DenDen047/WildPose_v1.1/wildpose/hardware/WLDPOSE011 Yaw shaft.SLDPRT

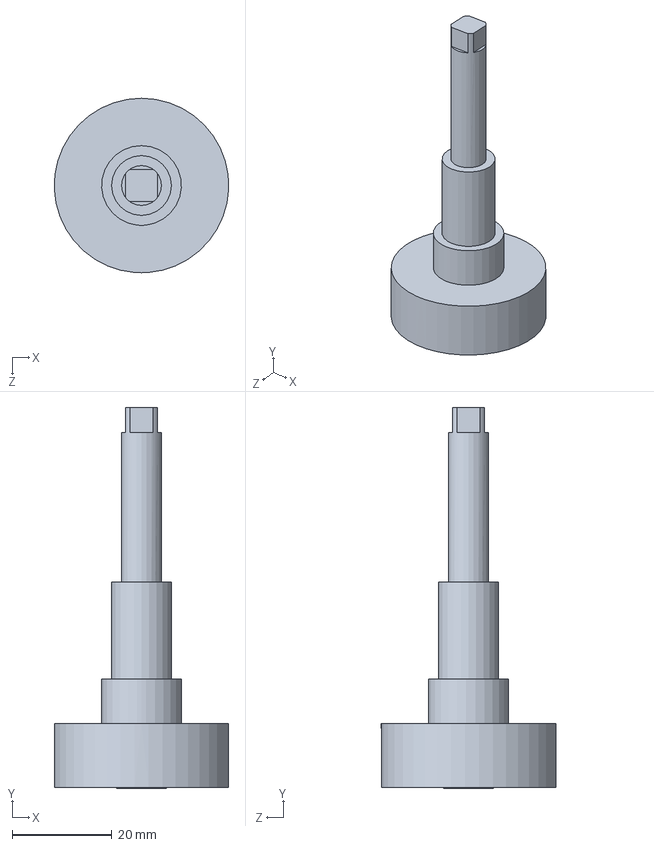
[picture p13: CAD file, 2025-09-01]
wildpose/hardware/WLDPOSE011 Yaw shaft.SLDPRT
35.0 x 76.4 x 35.0 mm
