DenDen047/WildPose_v1.1/wildpose/hardware/WLDPOSE006 Shaft Holder.SLDPRT

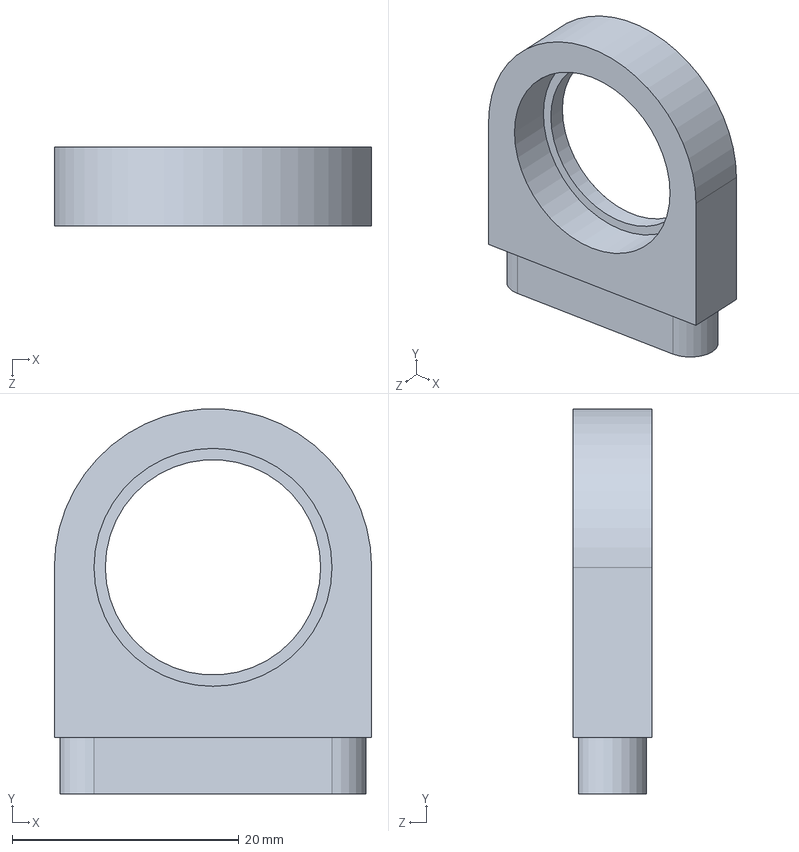
[picture p14: CAD file, 2025-09-01]
wildpose/hardware/WLDPOSE006 Shaft Holder.SLDPRT
28.0 x 34.0 x 7.00 mm
