DenDen047/WildPose_v1.1/wildpose/hardware/Timing Belt 80 T 162.56mm x 6mm.SLDPRT

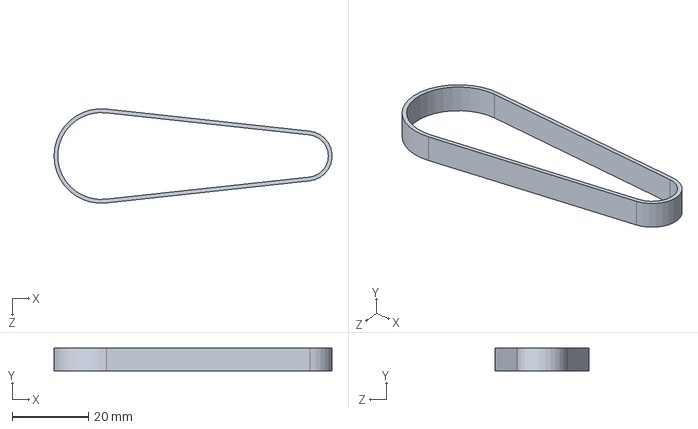
[picture p15: CAD file, 2025-09-01]
wildpose/hardware/Timing Belt 80 T 162.56mm x 6mm.SLDPRT
72.9 x 6.00 x 24.7 mm
