DenDen047/WildPose_v1.1/wildpose/hardware/HandleRod.SLDPRT

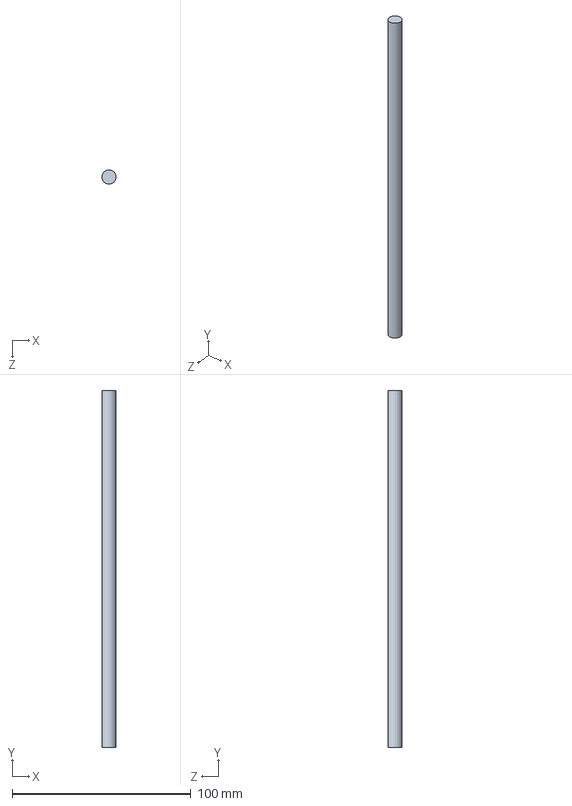
[picture p16: CAD file, 2025-09-01]
wildpose/hardware/HandleRod.SLDPRT
8.00 x 200.0 x 8.00 mm
