DenDen047/WildPose_v1.1/wildpose/hardware/Motor Mount.SLDPRT

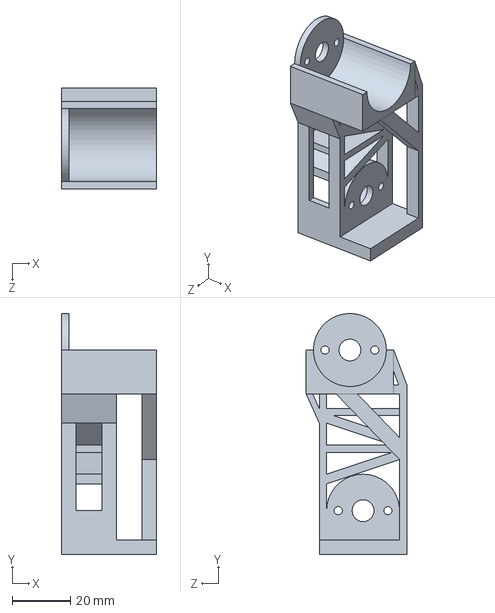
[picture p17: CAD file, 2025-09-01]
wildpose/hardware/Motor Mount.SLDPRT
32.5 x 82.5 x 34.5 mm
