DenDen047/WildPose_v1.1/wildpose/hardware/Pitch Encoder Holder (Printed).SLDPRT

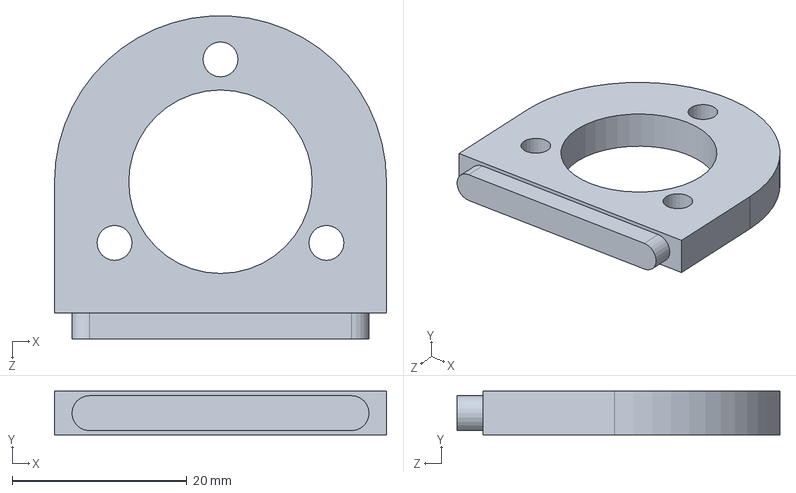
[picture p18: CAD file, 2025-09-01]
wildpose/hardware/Pitch Encoder Holder (Printed).SLDPRT
38.0 x 5.00 x 37.0 mm
