DenDen047/WildPose_v1.1/wildpose/hardware/Motor Belt.SLDPRT

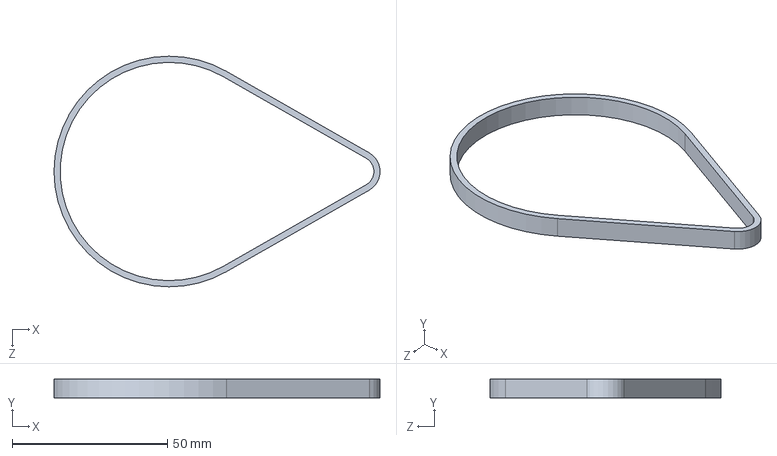
[picture p19: CAD file, 2025-09-01]
wildpose/hardware/Motor Belt.SLDPRT
105.0 x 6.00 x 74.3 mm
