DenDen047/WildPose_v1.1/wildpose/hardware/Xavier Holder.SLDPRT

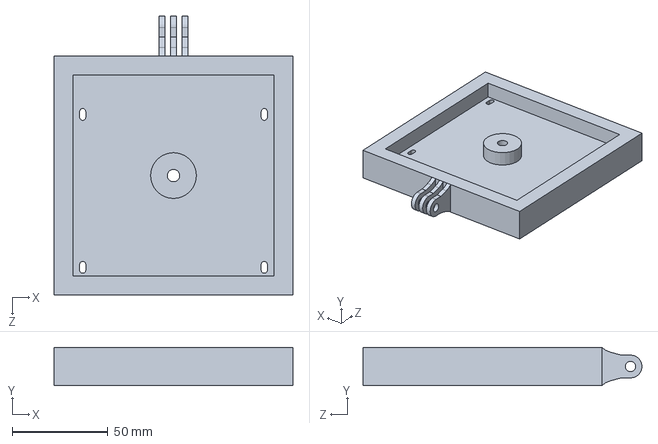
[picture p20: CAD file, 2025-09-01]
wildpose/hardware/Xavier Holder.SLDPRT
125.0 x 20.0 x 146.0 mm
