DenDen047/WildPose_v1.1/wildpose/hardware/WLDPOSE008 Pitch Shaft Connector v2.SLDPRT

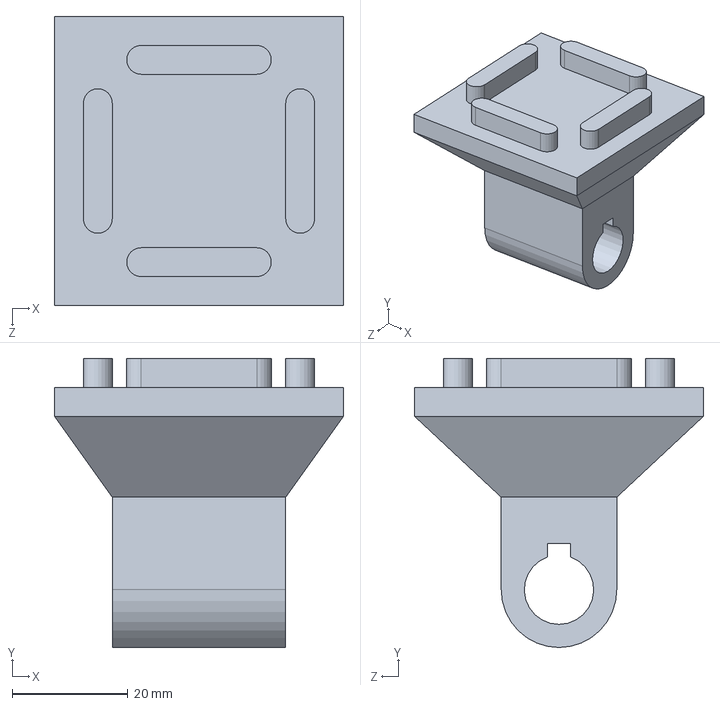
[picture p21: CAD file, 2025-09-01]
wildpose/hardware/WLDPOSE008 Pitch Shaft Connector v2.SLDPRT
50.0 x 50.0 x 50.0 mm
