DenDen047/WildPose_v1.1/wildpose/hardware/WLDPOSE003 Base Shaft Support Slot.SLDPRT

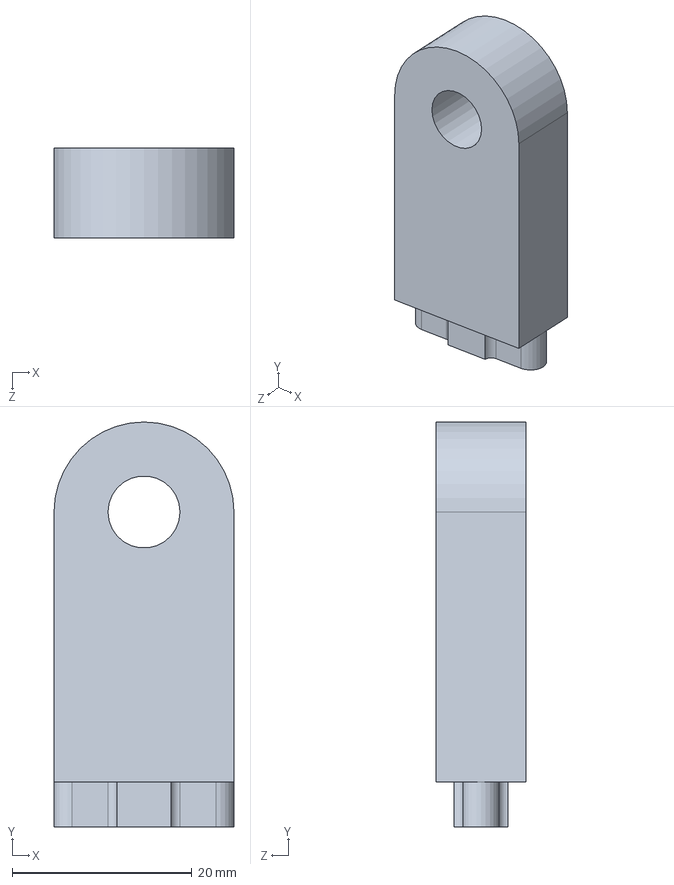
[picture p22: CAD file, 2025-09-01]
wildpose/hardware/WLDPOSE003 Base Shaft Support Slot.SLDPRT
20.0 x 45.0 x 10.0 mm
