DenDen047/WildPose_v1.1/wildpose/hardware/Ximea Holder.SLDPRT

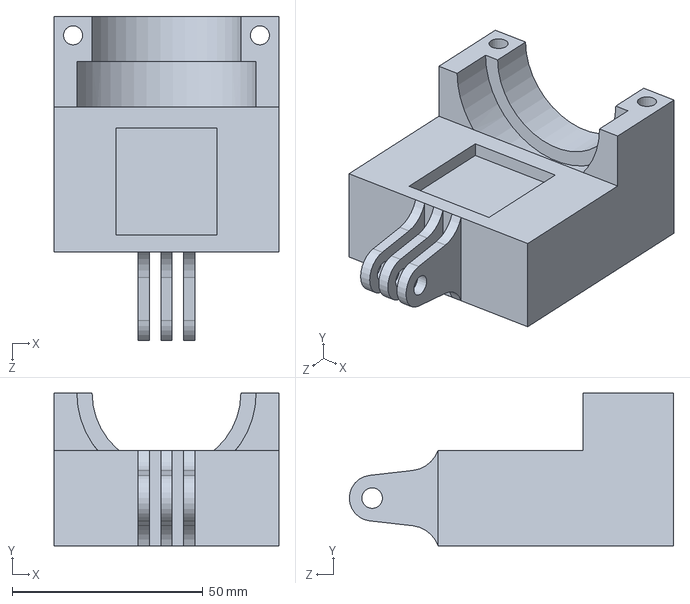
[picture p23: CAD file, 2025-09-01]
wildpose/hardware/Ximea Holder.SLDPRT
59.0 x 40.0 x 85.1 mm
