DenDen047/WildPose_v1.1/wildpose/hardware/Lens Support.SLDPRT

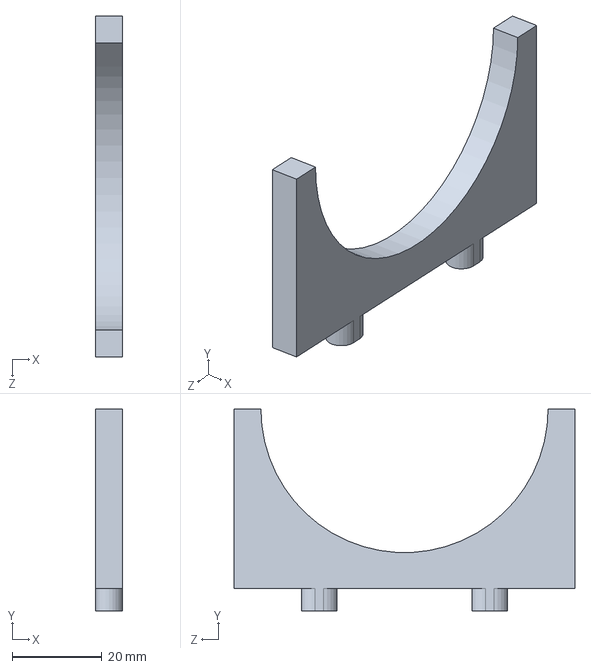
[picture p24: CAD file, 2025-09-01]
wildpose/hardware/Lens Support.SLDPRT
6.00 x 45.0 x 76.0 mm
