DenDen047/WildPose_v1.1/wildpose/hardware/Lens.SLDPRT

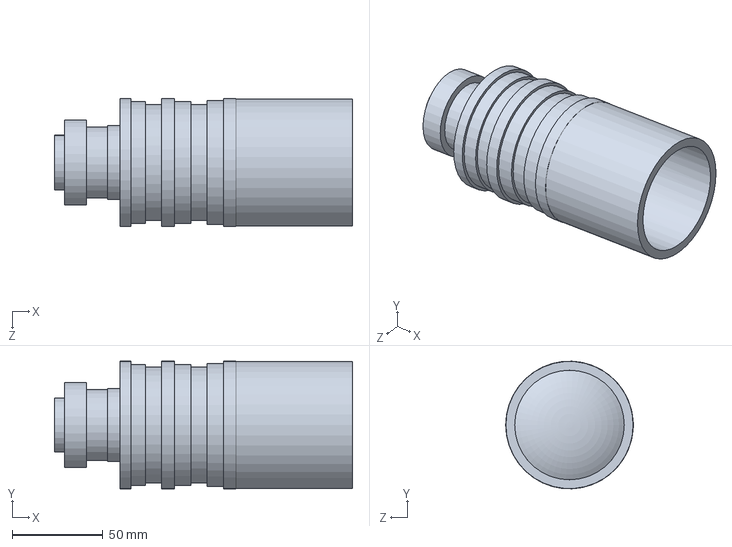
[picture p25: CAD file, 2025-09-01]
wildpose/hardware/Lens.SLDPRT
164.0 x 70.2 x 70.3 mm
