DenDen047/WildPose_v1.1/wildpose/hardware/WLDPOSE002 Base Bilot.SLDPRT

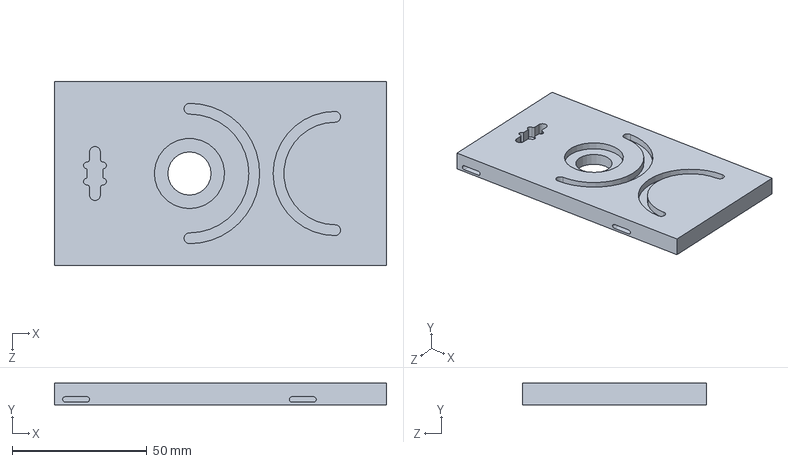
[picture p26: CAD file, 2025-09-01]
wildpose/hardware/WLDPOSE002 Base Bilot.SLDPRT
123.0 x 8.00 x 68.0 mm
