DenDen047/WildPose_v1.1/wildpose/hardware/WLDPOSE004 Bearing Holder.SLDPRT

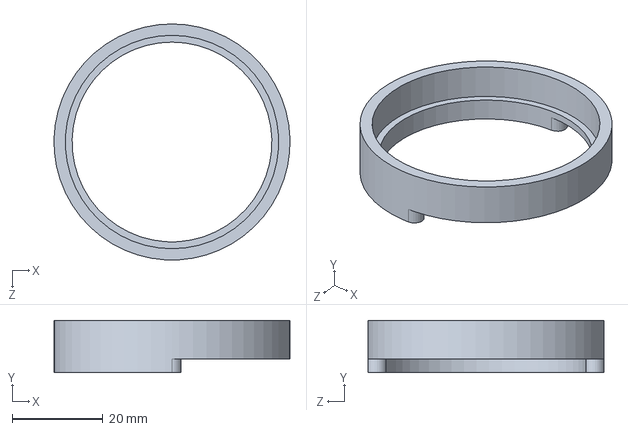
[picture p27: CAD file, 2025-09-01]
wildpose/hardware/WLDPOSE004 Bearing Holder.SLDPRT
52.0 x 11.5 x 52.0 mm
