DenDen047/WildPose_v1.1/wildpose/hardware/Zimea Camera MQ022CG-CM.SLDPRT

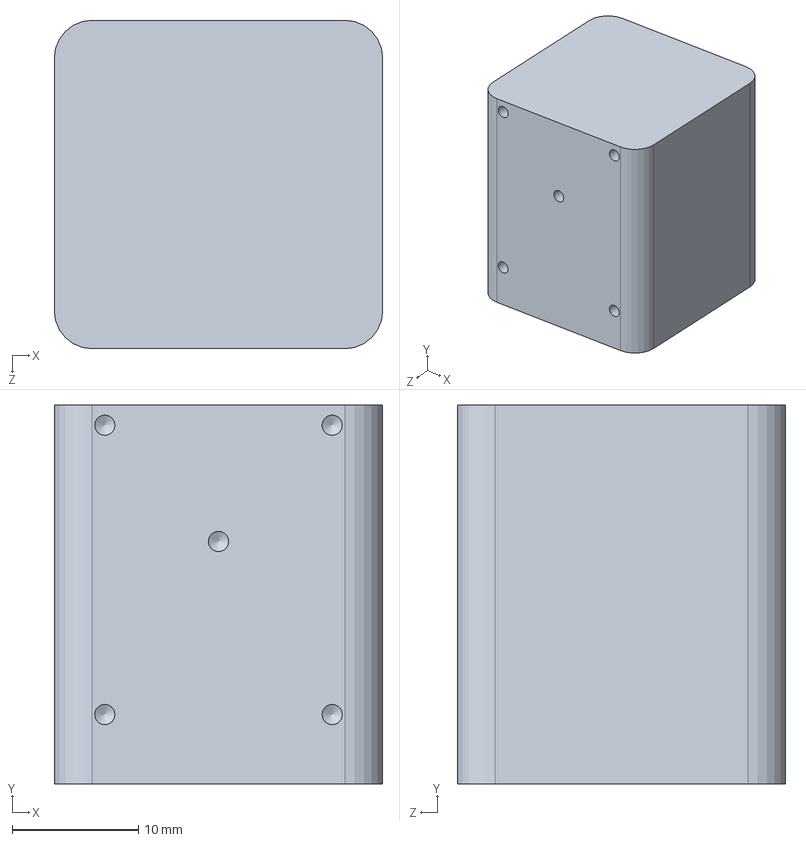
[picture p28: CAD file, 2025-09-01]
wildpose/hardware/Zimea Camera MQ022CG-CM.SLDPRT
26.0 x 30.0 x 26.0 mm
