DenDen047/WildPose_v1.1/wildpose/hardware/Screen Mount.SLDPRT

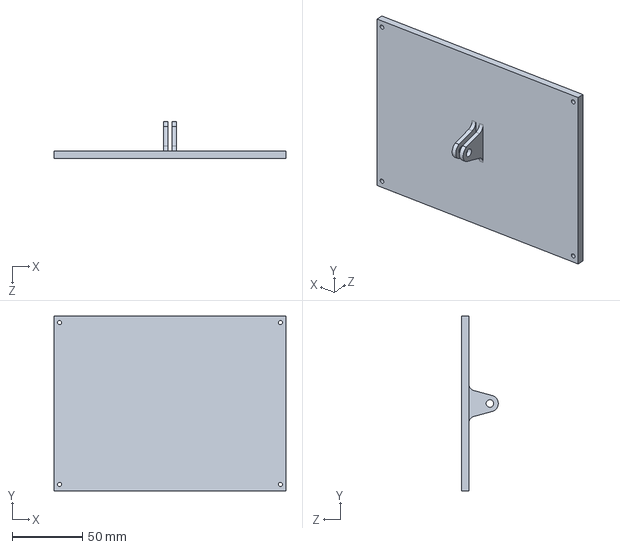
[picture p29: CAD file, 2025-09-01]
wildpose/hardware/Screen Mount.SLDPRT
164.9 x 124.2 x 26.0 mm
