DenDen047/WildPose_v1.1/wildpose/hardware/Camera Mount.SLDPRT

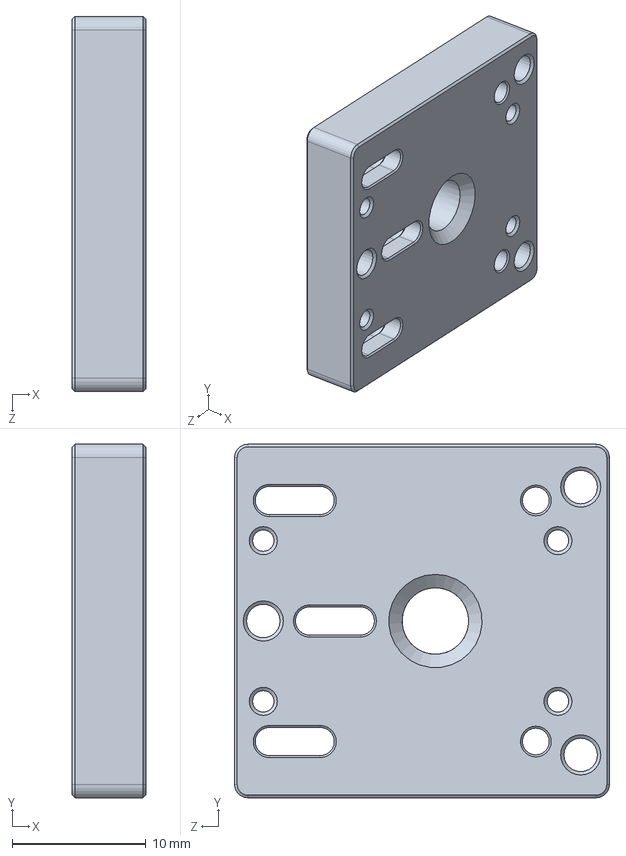
[picture p30: CAD file, 2025-09-01]
wildpose/hardware/Camera Mount.SLDPRT
5.50 x 26.4 x 28.0 mm
