DenDen047/WildPose_v1.1/wildpose/hardware/18 T 2.032mm P , 6mm W Pulley.SLDPRT

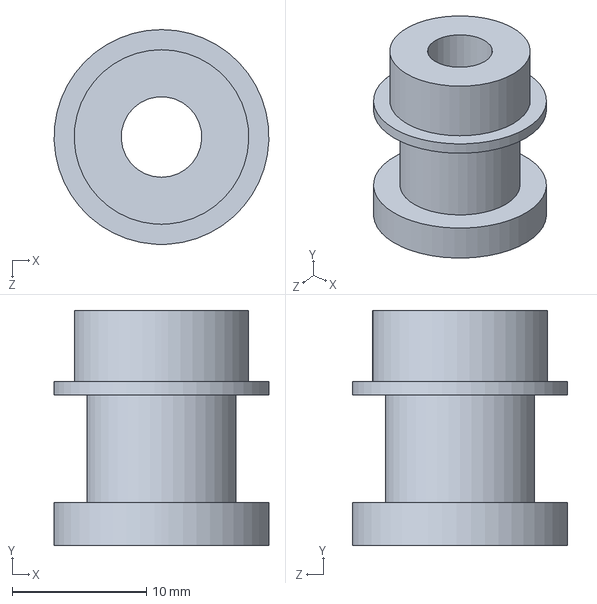
[picture p31: CAD file, 2025-09-01]
wildpose/hardware/18 T 2.032mm P , 6mm W Pulley.SLDPRT
16.0 x 17.5 x 16.0 mm
