DenDen047/WildPose_v1.1/wildpose/hardware/25d-metal-gearmotor-75-99-encoder.step.SLDPRT

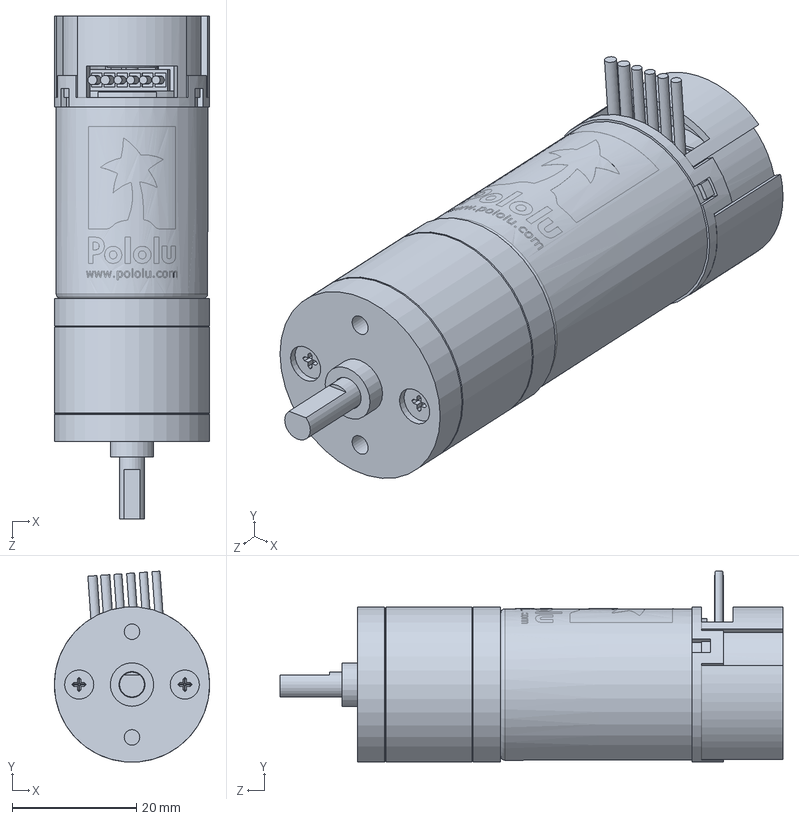
[picture p32: CAD file, 2025-09-01]
wildpose/hardware/25d-metal-gearmotor-75-99-encoder.step.SLDPRT
25.0 x 30.7 x 80.9 mm
