DenDen047/WildPose_v1.1/wildpose/hardware/Belt Pulley 778-4828.SLDPRT

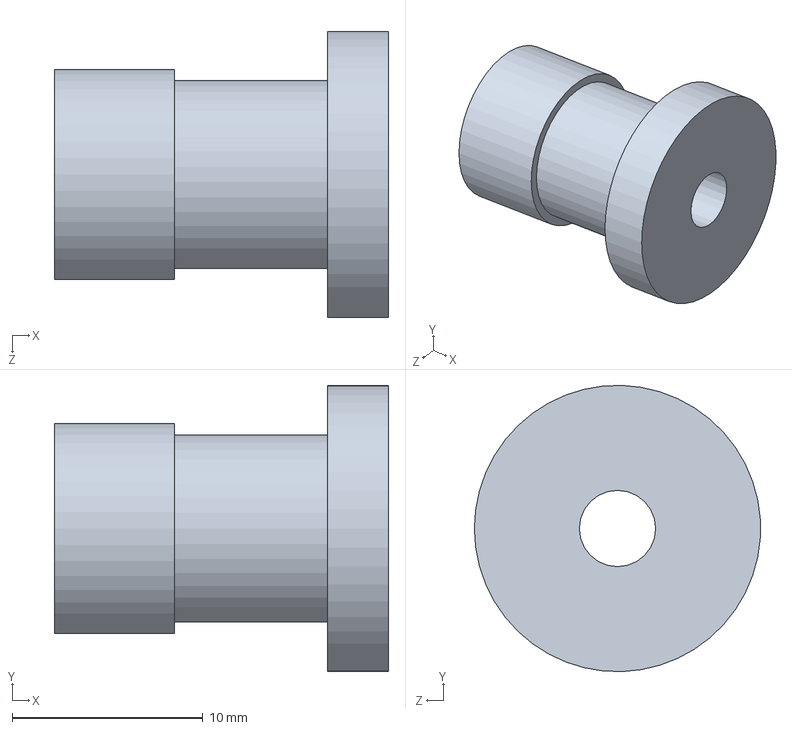
[picture p33: CAD file, 2025-09-01]
wildpose/hardware/Belt Pulley 778-4828.SLDPRT
17.5 x 15.0 x 15.0 mm
