DenDen047/WildPose_v1.1/wildpose/hardware/Nvidea Xavier.SLDPRT

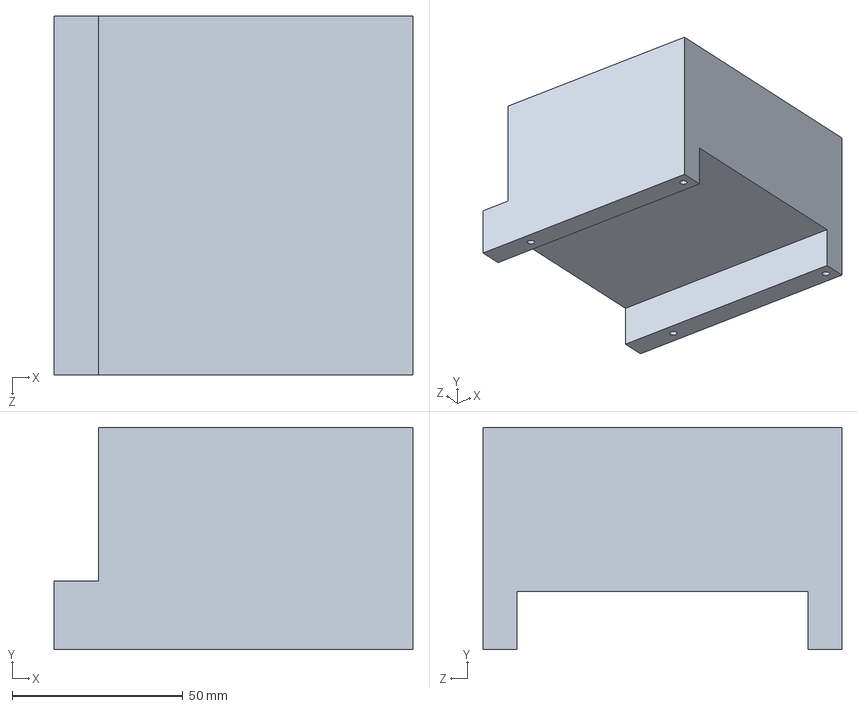
[picture p34: CAD file, 2025-09-01]
wildpose/hardware/Nvidea Xavier.SLDPRT
105.0 x 65.0 x 105.0 mm
