DenDen047/WildPose_v1.1/wildpose/hardware/WLDPOSE001 Base Wing Slots.SLDPRT

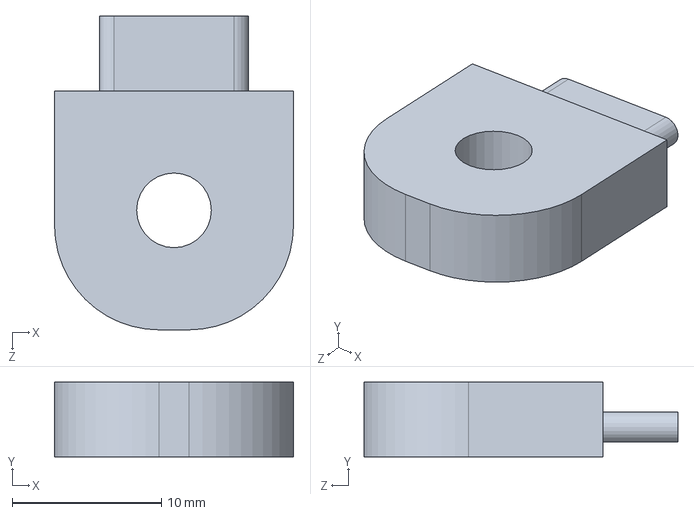
[picture p35: CAD file, 2025-09-01]
wildpose/hardware/WLDPOSE001 Base Wing Slots.SLDPRT
16.0 x 5.00 x 21.0 mm
