DenDen047/WildPose_v1.1/wildpose/hardware/Base Encoder Holder (Printed).SLDPRT

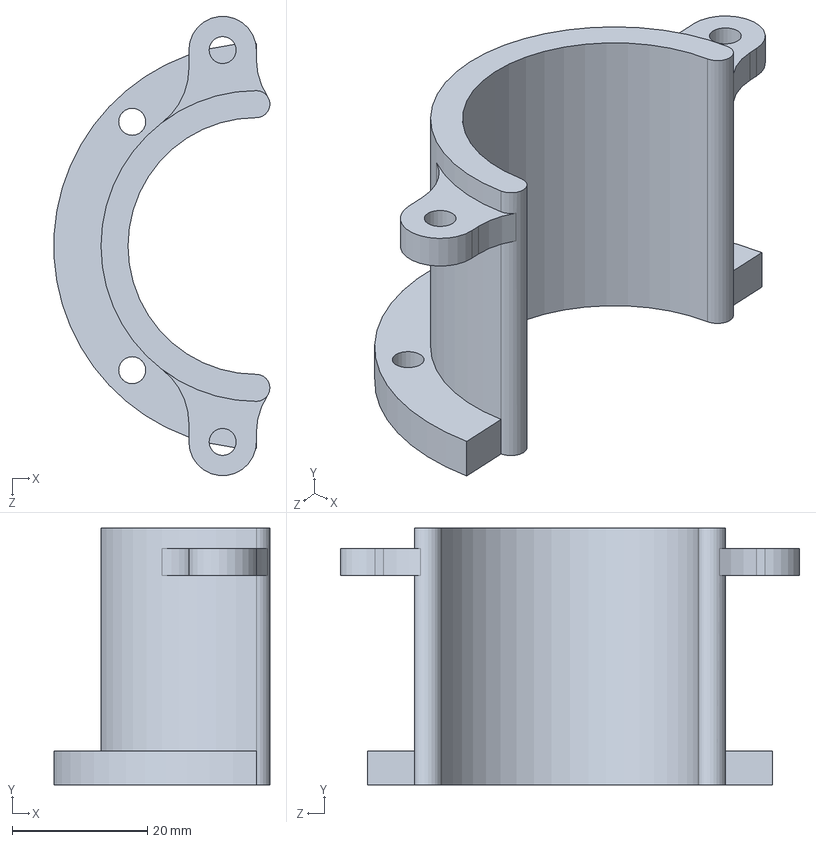
[picture p36: CAD file, 2025-09-01]
wildpose/hardware/Base Encoder Holder (Printed).SLDPRT
31.9 x 38.0 x 67.9 mm
