DenDen047/WildPose_v1.1/wildpose/hardware/WLDPOSE005 Pitch Bilot.SLDPRT

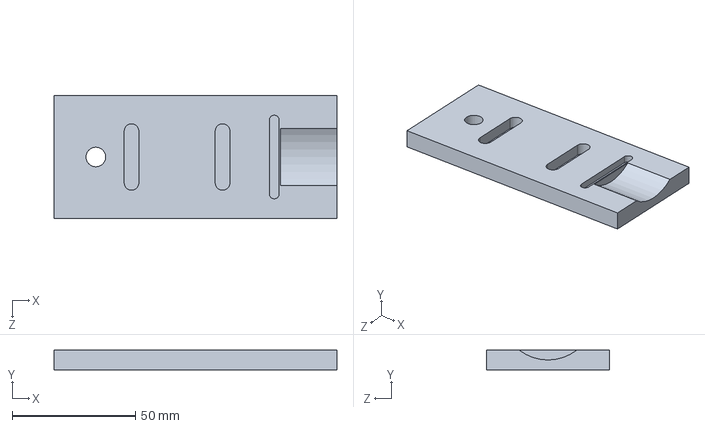
[picture p37: CAD file, 2025-09-01]
wildpose/hardware/WLDPOSE005 Pitch Bilot.SLDPRT
115.0 x 8.00 x 50.0 mm
