DenDen047/WildPose_v1.1/wildpose/hardware/QLED Screen.SLDPRT

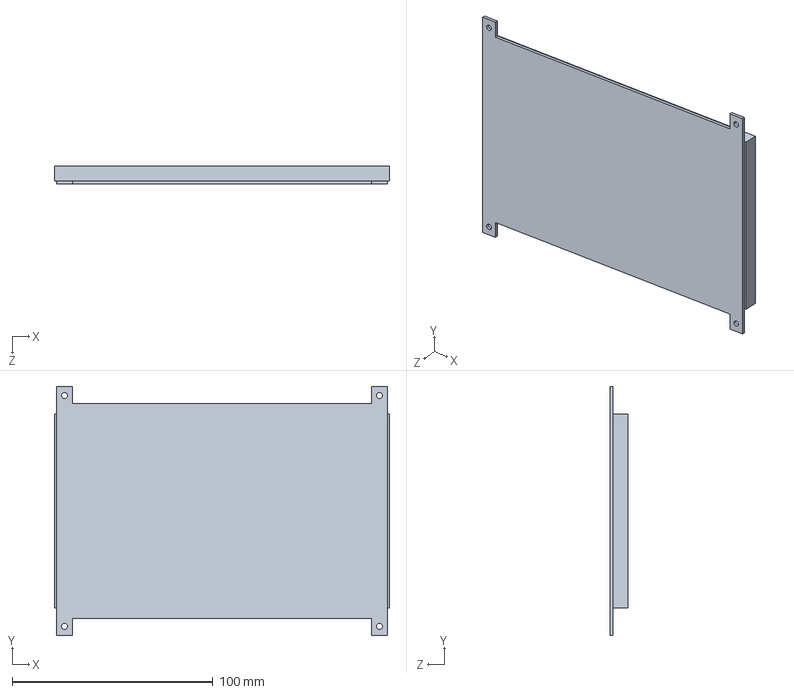
[picture p38: CAD file, 2025-09-01]
wildpose/hardware/QLED Screen.SLDPRT
166.9 x 124.3 x 9.10 mm
