DenDen047/WildPose_v1.1/wildpose/hardware/WLDPOSE008 Pitch Shaft Connector.SLDPRT

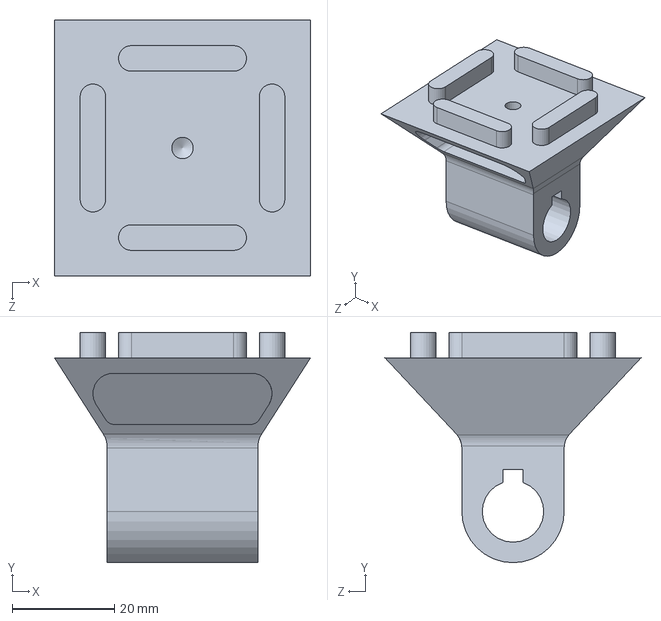
[picture p39: CAD file, 2025-09-01]
wildpose/hardware/WLDPOSE008 Pitch Shaft Connector.SLDPRT
50.0 x 45.0 x 50.0 mm
